CoryParsnipson/rpi-proto-1/models/chassis-v2/charger-mounting-bracket.FCStd

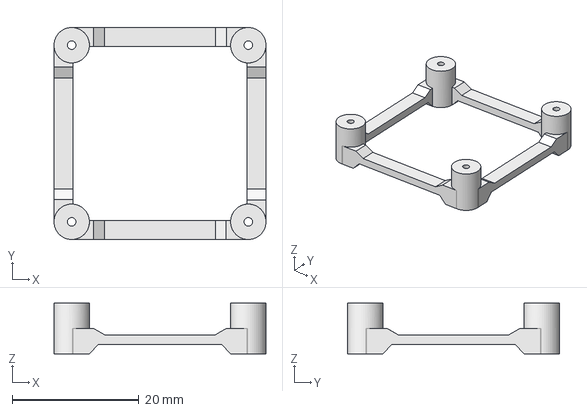
[picture p15: CAD file, 2021-10-05]
models/chassis-v2/charger-mounting-bracket.FCStd
33.5 x 33.5 x 8.00 mm
