CoryParsnipson/rpi-proto-1/models/controller-chassis-mount-left/dpad_undercarriage.FCStd

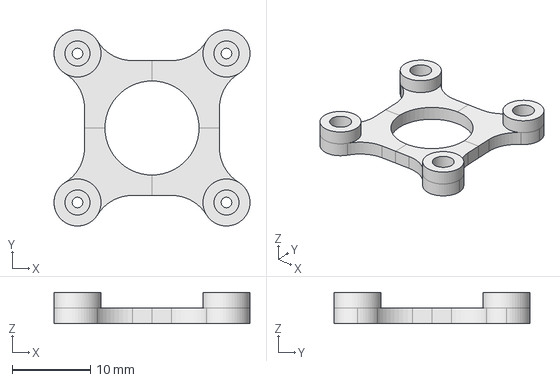
[picture p16: CAD file, 2021-06-01]
models/controller-chassis-mount-left/dpad_undercarriage.FCStd
25.0 x 25.0 x 4.00 mm
