CoryParsnipson/rpi-proto-1/models/controller-chassis-mount-right/prusa_mk3_settings.3mf

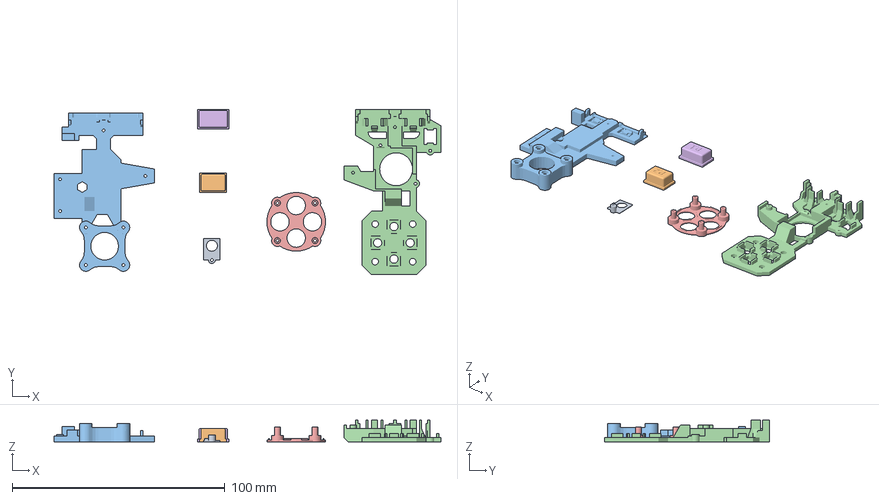
[picture p17: CAD file, 2021-05-28]
models/controller-chassis-mount-right/prusa_mk3_settings.3mf
182.1 x 77.9 x 10.1 mm
select-button-holder.stl
R2-button.stl
bottom-plate.stl
top-plate.stl
button-holder.stl
R1-button.stl
