CoryParsnipson/rpi-proto-1/models/dpad_tactile/dpad_tactile_cover.FCStd

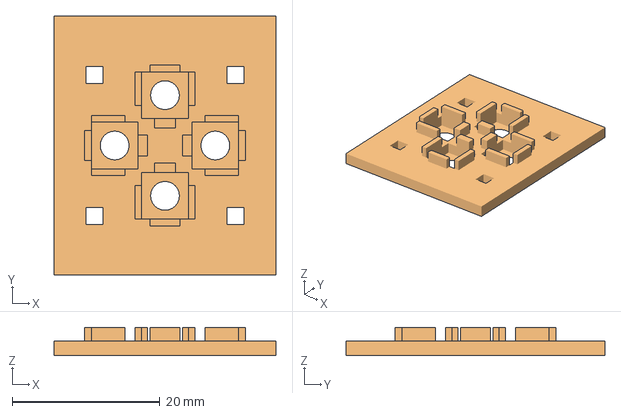
[picture p18: CAD file, 2021-04-29]
models/dpad_tactile/dpad_tactile_cover.FCStd
30.0 x 35.0 x 3.85 mm
Fiduciary Hole Polar Pattern (Meshed)
