CoryParsnipson/rpi-proto-1/models/enclosure-v1/back-cover.FCStd

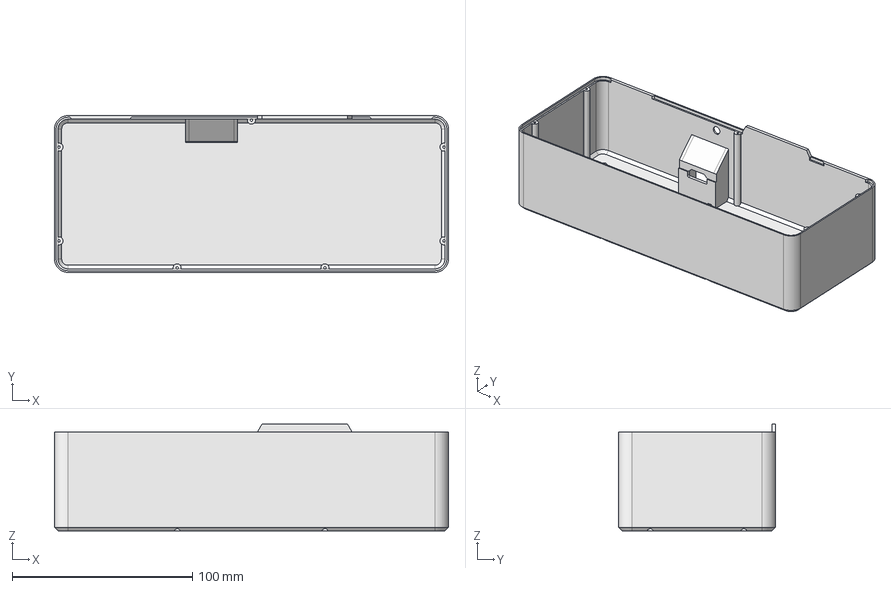
[picture p19: CAD file, 2021-11-22]
models/enclosure-v1/back-cover.FCStd
218.6 x 87.0 x 59.3 mm
