CoryParsnipson/rpi-proto-1/models/shoulder-buttons-left-v2/bottom-holder.FCStd

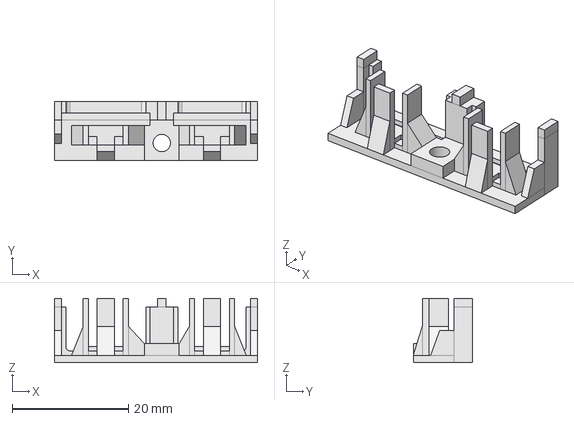
[picture p20: CAD file, 2021-05-08]
models/shoulder-buttons-left-v2/bottom-holder.FCStd
35.0 x 10.2 x 11.1 mm
