CoryParsnipson/rpi-proto-1/models/chassis-v2/second-tier-holder.FCStd

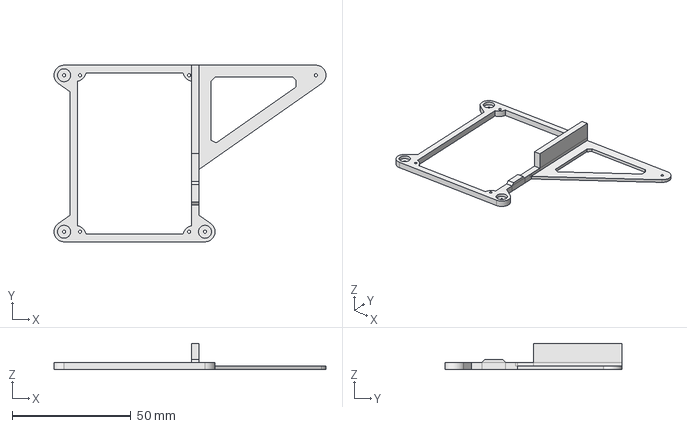
[picture p21: CAD file, 2021-10-05]
models/chassis-v2/second-tier-holder.FCStd
114.7 x 74.5 x 11.0 mm
