CoryParsnipson/rpi-proto-1/models/controller-chassis-mount-left/top-plate.FCStd

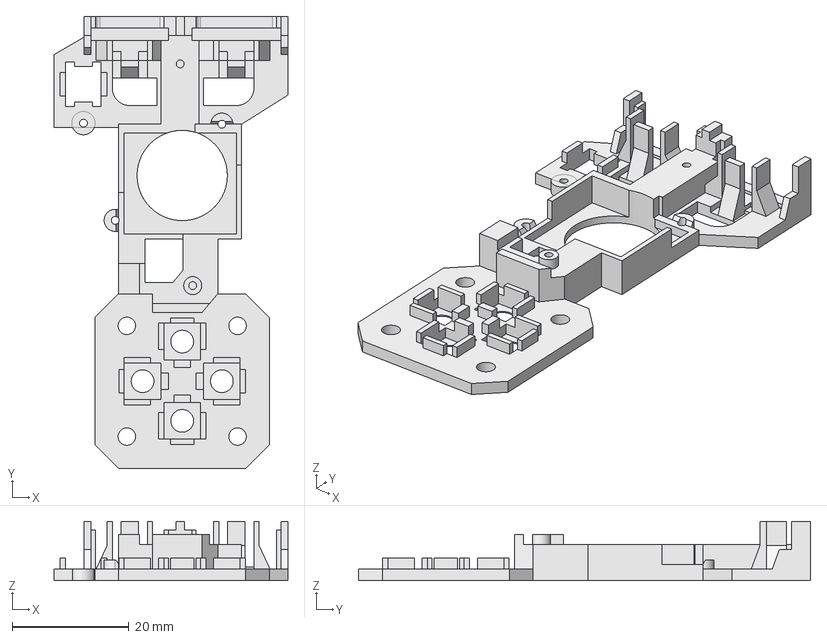
[picture p22: CAD file, 2021-05-31]
models/controller-chassis-mount-left/top-plate.FCStd
40.1 x 77.6 x 10.2 mm
