CoryParsnipson/rpi-proto-1/models/controller-chassis-mount-right/R1-button.FCStd

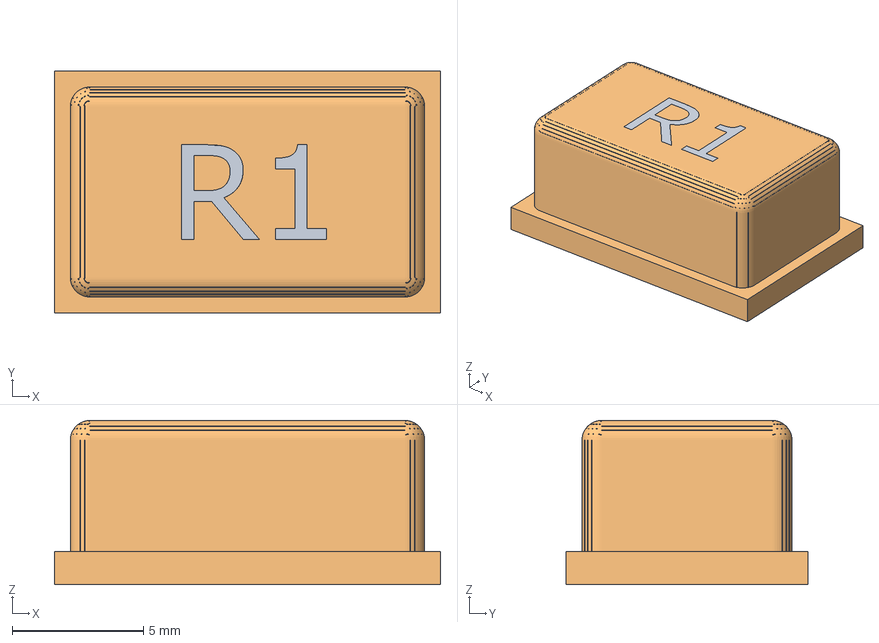
[picture p23: CAD file, 2021-05-26]
models/controller-chassis-mount-right/R1-button.FCStd
14.7 x 9.20 x 6.25 mm
Cut (Meshed)
