CoryParsnipson/rpi-proto-1/models/dpad_tactile/dpad_tactile_dpad_holder.FCStd

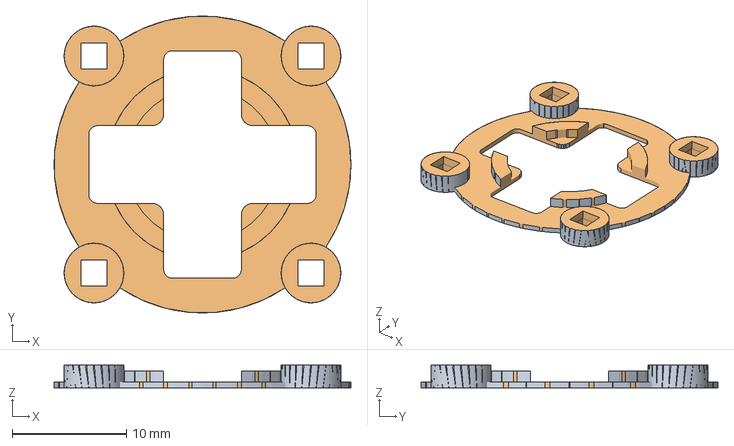
[picture p24: CAD file, 2021-04-29]
models/dpad_tactile/dpad_tactile_dpad_holder.FCStd
26.0 x 26.0 x 2.00 mm
Fiduciary Through Hole Chamfer Polar Pattern (Meshed)
