CoryParsnipson/rpi-proto-1/models/enclosure-v1/test-plate-connectors.FCStd

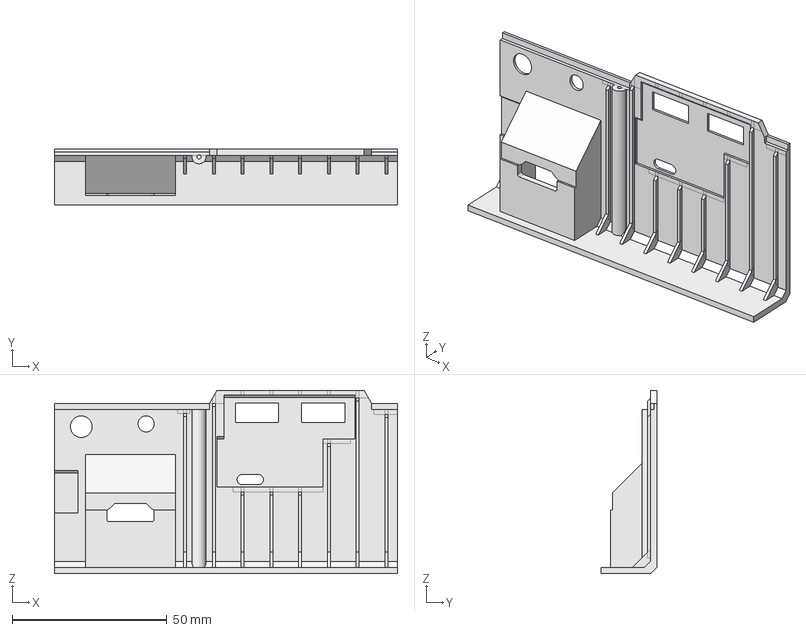
[picture p25: CAD file, 2021-11-21]
models/enclosure-v1/test-plate-connectors.FCStd
110.8 x 18.0 x 59.3 mm
