CoryParsnipson/rpi-proto-1/models/shoulder-buttons-left-v2/L2-button.FCStd

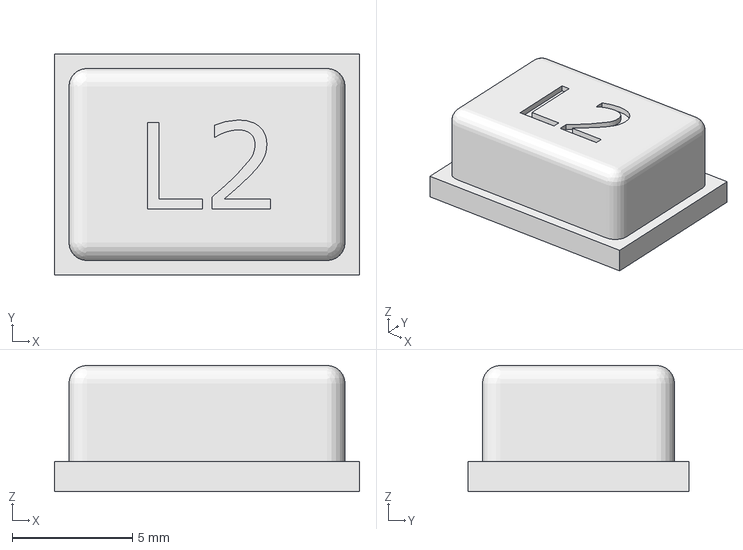
[picture p26: CAD file, 2021-05-08]
models/shoulder-buttons-left-v2/L2-button.FCStd
12.7 x 9.20 x 5.25 mm
