CoryParsnipson/rpi-proto-1/models/thumbstick-v2/thumbstick-holder-bottom.FCStd

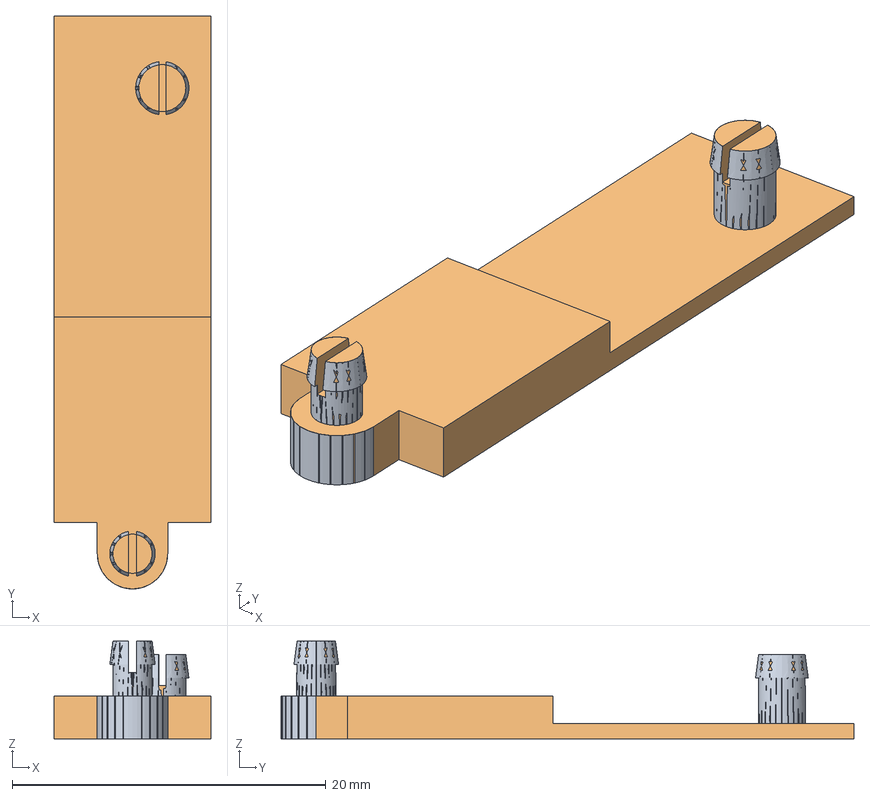
[picture p27: CAD file, 2021-05-05]
models/thumbstick-v2/thumbstick-holder-bottom.FCStd
10.0 x 36.5 x 6.25 mm
Pocket002 (Meshed)
