CoryParsnipson/rpi-proto-1/models/chassis-v2/second-tier-holder-v2.FCStd

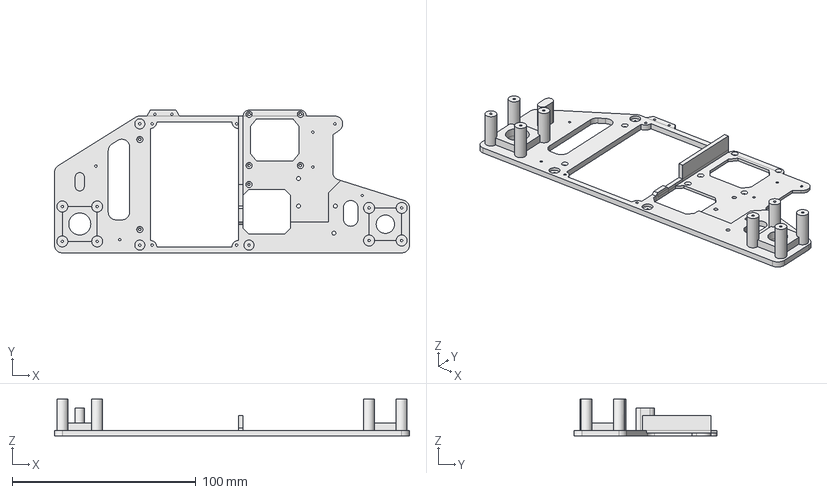
[picture p28: CAD file, 2021-10-05]
models/chassis-v2/second-tier-holder-v2.FCStd
193.2 x 77.8 x 20.0 mm
