CoryParsnipson/rpi-proto-1/models/controller-chassis-mount-left/dpad_holder.FCStd

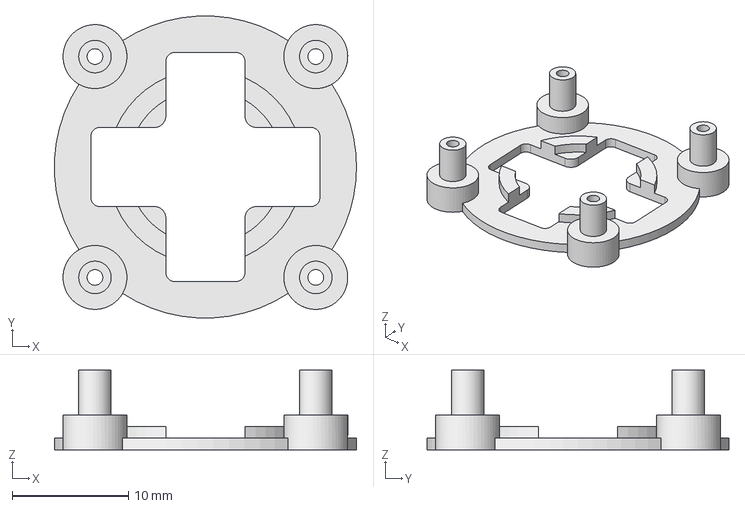
[picture p29: CAD file, 2021-05-15]
models/controller-chassis-mount-left/dpad_holder.FCStd
26.0 x 26.0 x 6.85 mm
