CoryParsnipson/rpi-proto-1/models/controller-chassis-mount-right/R2-button.FCStd

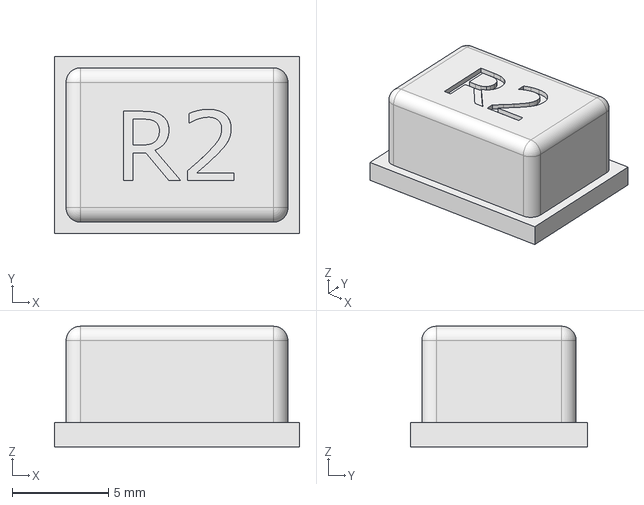
[picture p30: CAD file, 2021-05-26]
models/controller-chassis-mount-right/R2-button.FCStd
12.7 x 9.20 x 6.25 mm
