CoryParsnipson/rpi-proto-1/models/dpad_tactile/dpad_tactile_undercarriage.FCStd

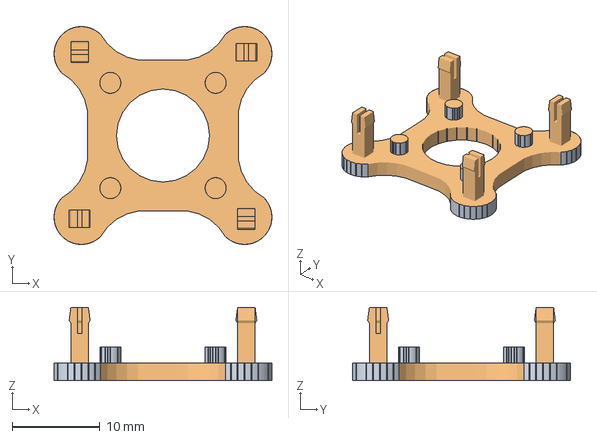
[picture p31: CAD file, 2021-04-29]
models/dpad_tactile/dpad_tactile_undercarriage.FCStd
24.8 x 24.8 x 8.35 mm
PolarPattern005 (Meshed)
