CoryParsnipson/rpi-proto-1/models/enclosure-v1/test-plate-hdmi-back.FCStd

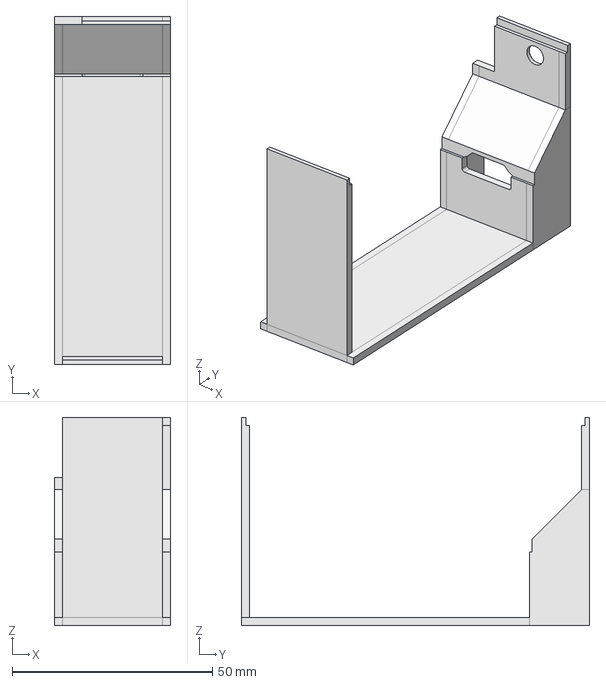
[picture p32: CAD file, 2021-11-18]
models/enclosure-v1/test-plate-hdmi-back.FCStd
29.0 x 87.0 x 52.0 mm
