CoryParsnipson/rpi-proto-1/models/shoulder-buttons-left-v2/top-holder.FCStd

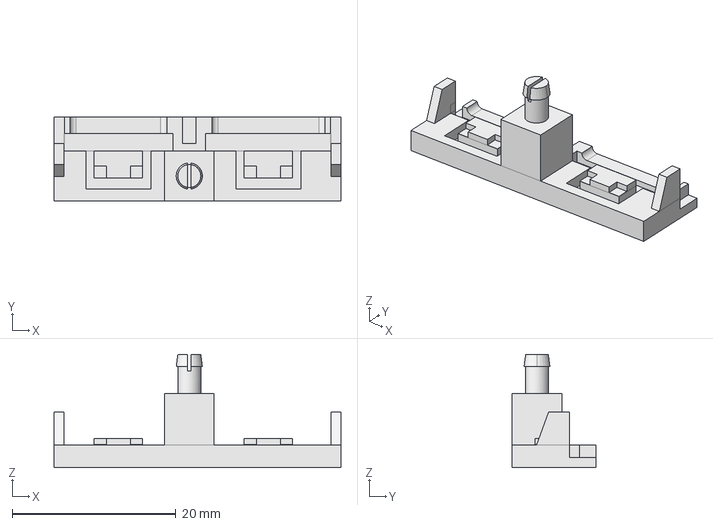
[picture p33: CAD file, 2021-05-08]
models/shoulder-buttons-left-v2/top-holder.FCStd
35.0 x 10.2 x 13.8 mm
