CoryParsnipson/rpi-proto-1/models/thumbstick-v2/thumbstick-holder-v2.3mf

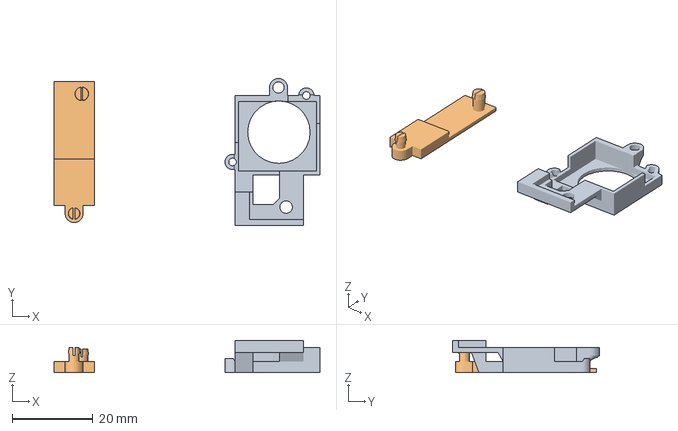
[picture p34: CAD file, 2021-05-04]
models/thumbstick-v2/thumbstick-holder-v2.3mf
66.0 x 36.5 x 8.00 mm
thumbstick-holder-v2.stl
thumbstick-holder-v2-bottom.stl
