CoryParsnipson/rpi-proto-1/models/chassis-v2/power-switch-holder.FCStd

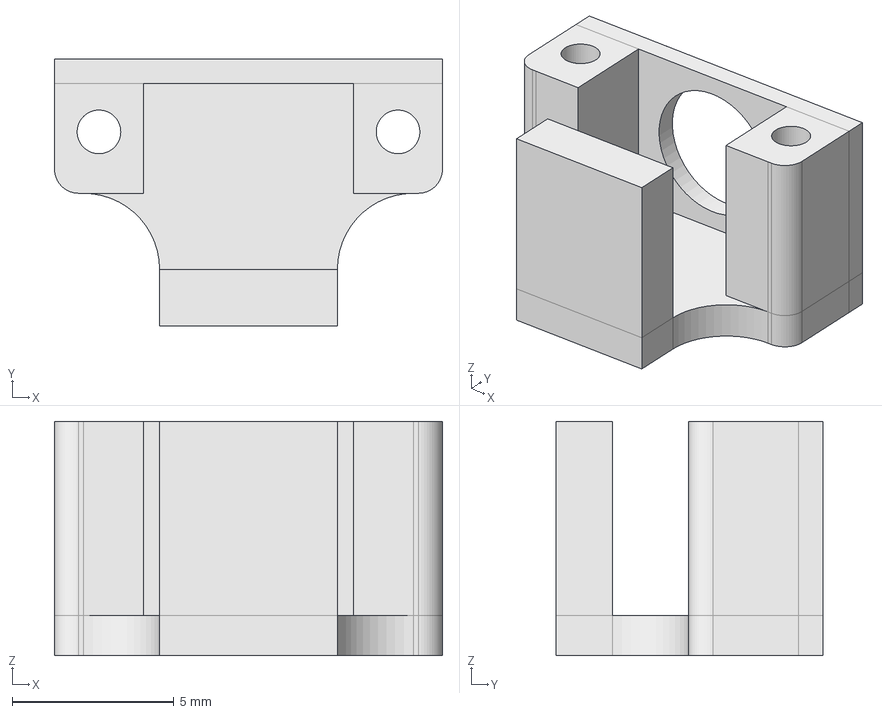
[picture p35: CAD file, 2021-10-05]
models/chassis-v2/power-switch-holder.FCStd
12.0 x 8.25 x 7.25 mm
