CoryParsnipson/rpi-proto-1/models/controller-chassis-mount-left/select-button-holder.FCStd

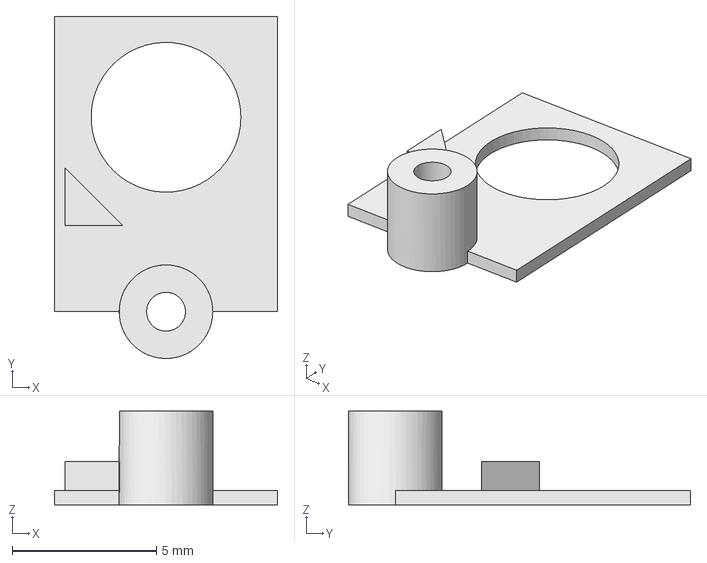
[picture p36: CAD file, 2021-05-15]
models/controller-chassis-mount-left/select-button-holder.FCStd
7.75 x 11.9 x 3.25 mm
