CoryParsnipson/rpi-proto-1/models/controller-chassis-mount-right/abxy-undercarriage.FCStd

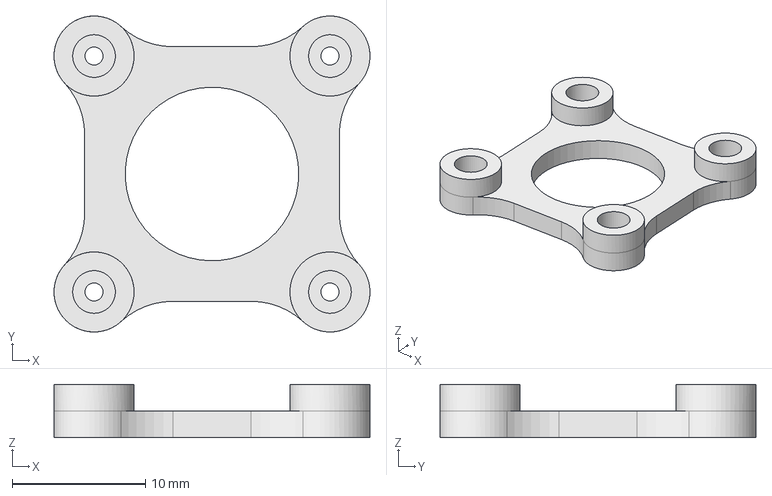
[picture p37: CAD file, 2021-05-24]
models/controller-chassis-mount-right/abxy-undercarriage.FCStd
23.7 x 23.7 x 4.00 mm
