CoryParsnipson/rpi-proto-1/models/enclosure-v1/test-plate-hdmi-back-2.FCStd

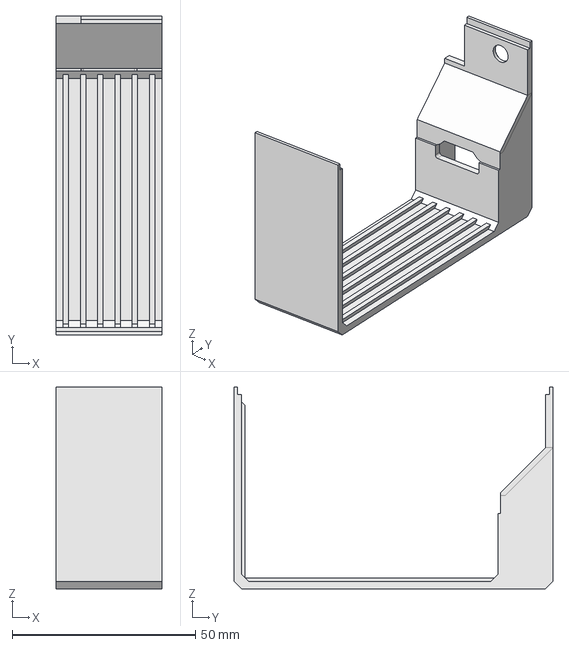
[picture p38: CAD file, 2021-11-18]
models/enclosure-v1/test-plate-hdmi-back-2.FCStd
29.0 x 87.0 x 55.0 mm
