CoryParsnipson/rpi-proto-1/models/thumbstick-v2/thumbstick-holder.FCStd

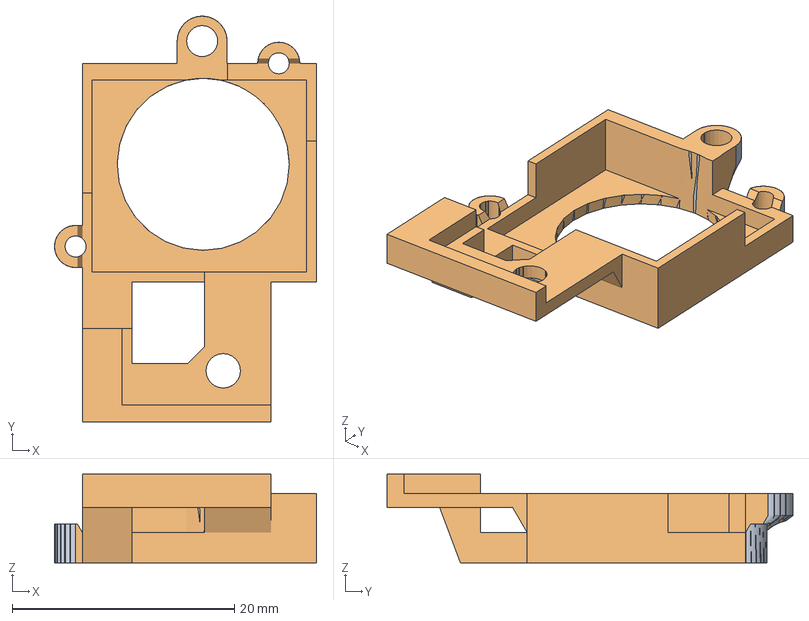
[picture p39: CAD file, 2021-05-04]
models/thumbstick-v2/thumbstick-holder.FCStd
23.6 x 36.5 x 8.00 mm
Pocket009 (Meshed)
