CoryParsnipson/rpi-proto-1/models/chassis-v2/screen-backing.FCStd

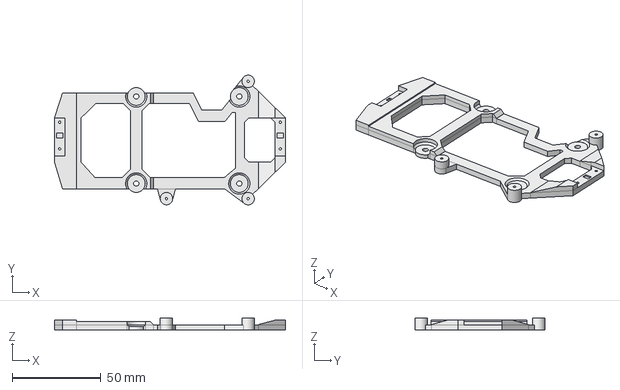
[picture p40: CAD file, 2021-06-09]
models/chassis-v2/screen-backing.FCStd
130.0 x 73.0 x 7.00 mm
