CoryParsnipson/rpi-proto-1/models/controller-chassis-mount-left/L2-button.FCStd

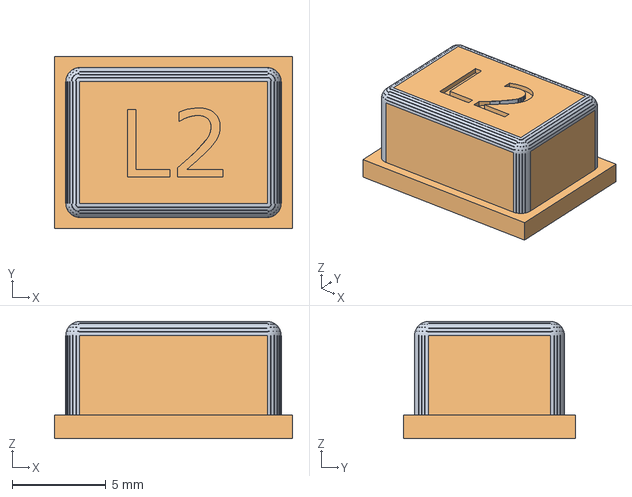
[picture p41: CAD file, 2021-05-15]
models/controller-chassis-mount-left/L2-button.FCStd
12.7 x 9.20 x 6.25 mm
Cut (Meshed)
