CoryParsnipson/rpi-proto-1/models/enclosure-v1/front-cover.FCStd

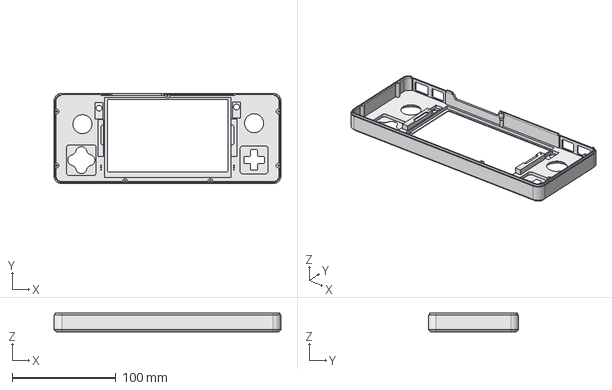
[picture p42: CAD file, 2021-11-08]
models/enclosure-v1/front-cover.FCStd
218.6 x 87.0 x 18.0 mm
