CoryParsnipson/rpi-proto-1/models/controller-chassis-mount-left/L1-button.FCStd

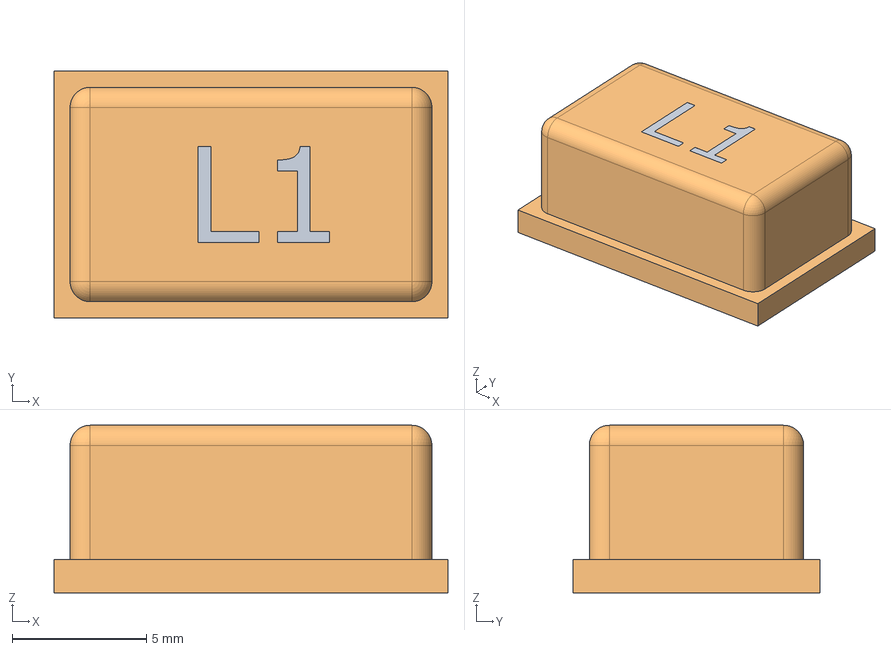
[picture p43: CAD file, 2021-05-15]
models/controller-chassis-mount-left/L1-button.FCStd
14.7 x 9.20 x 6.25 mm
