CoryParsnipson/rpi-proto-1/models/enclosure-v1/test-plate-left-controller-2.FCStd

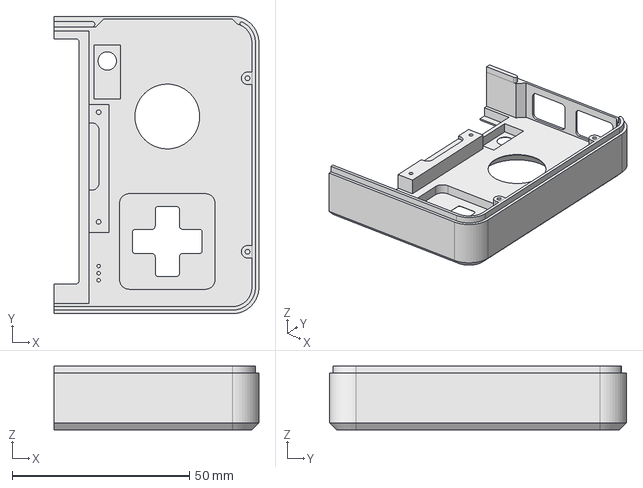
[picture p44: CAD file, 2021-10-30]
models/enclosure-v1/test-plate-left-controller-2.FCStd
57.9 x 84.0 x 18.0 mm
