CoryParsnipson/rpi-proto-1/models/enclosure-v1/test-plate-thickness.FCStd

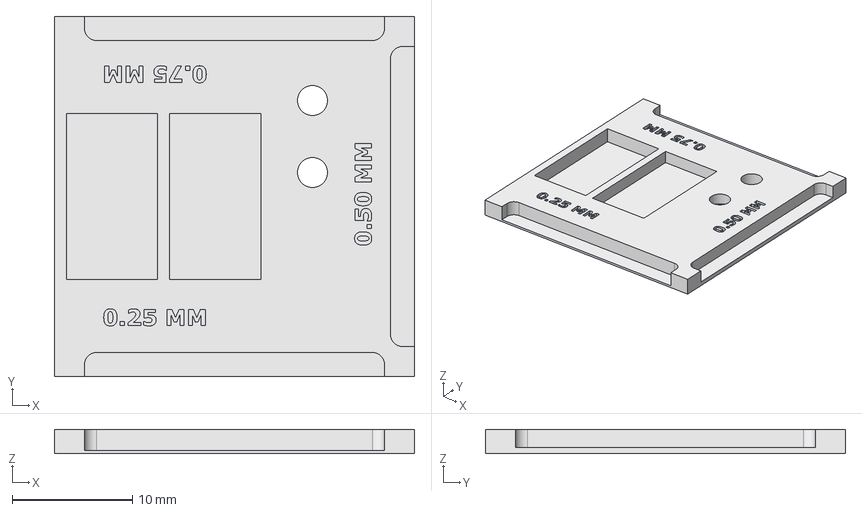
[picture p45: CAD file, 2021-10-26]
models/enclosure-v1/test-plate-thickness.FCStd
30.0 x 30.0 x 2.00 mm
