CoryParsnipson/rpi-proto-1/models/enclosure-v1/test-plate-left-controller.FCStd

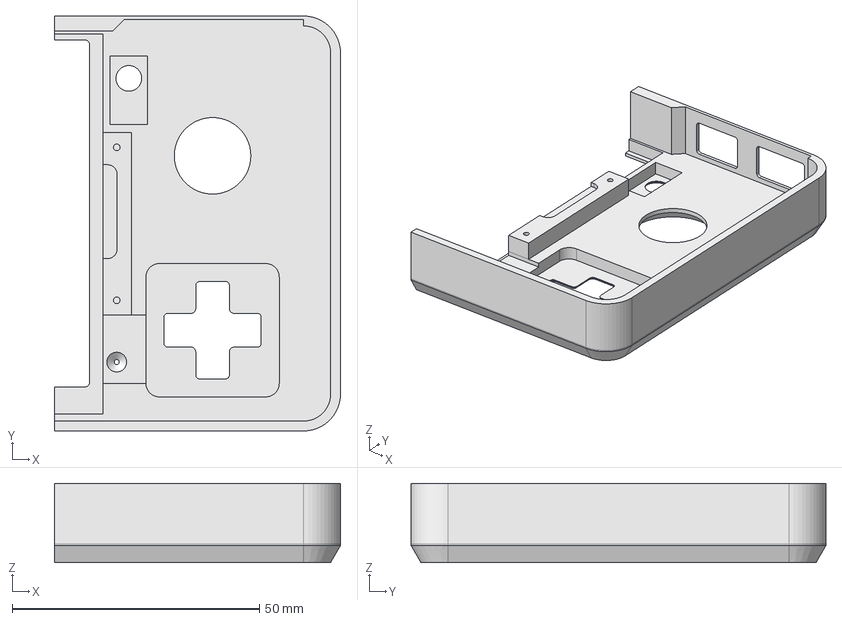
[picture p46: CAD file, 2021-10-22]
models/enclosure-v1/test-plate-left-controller.FCStd
57.9 x 84.0 x 16.0 mm
